Alectardy98/aek/aek.kicad_sch

## KiCad design aek.kicad_sch (2023-07-03)

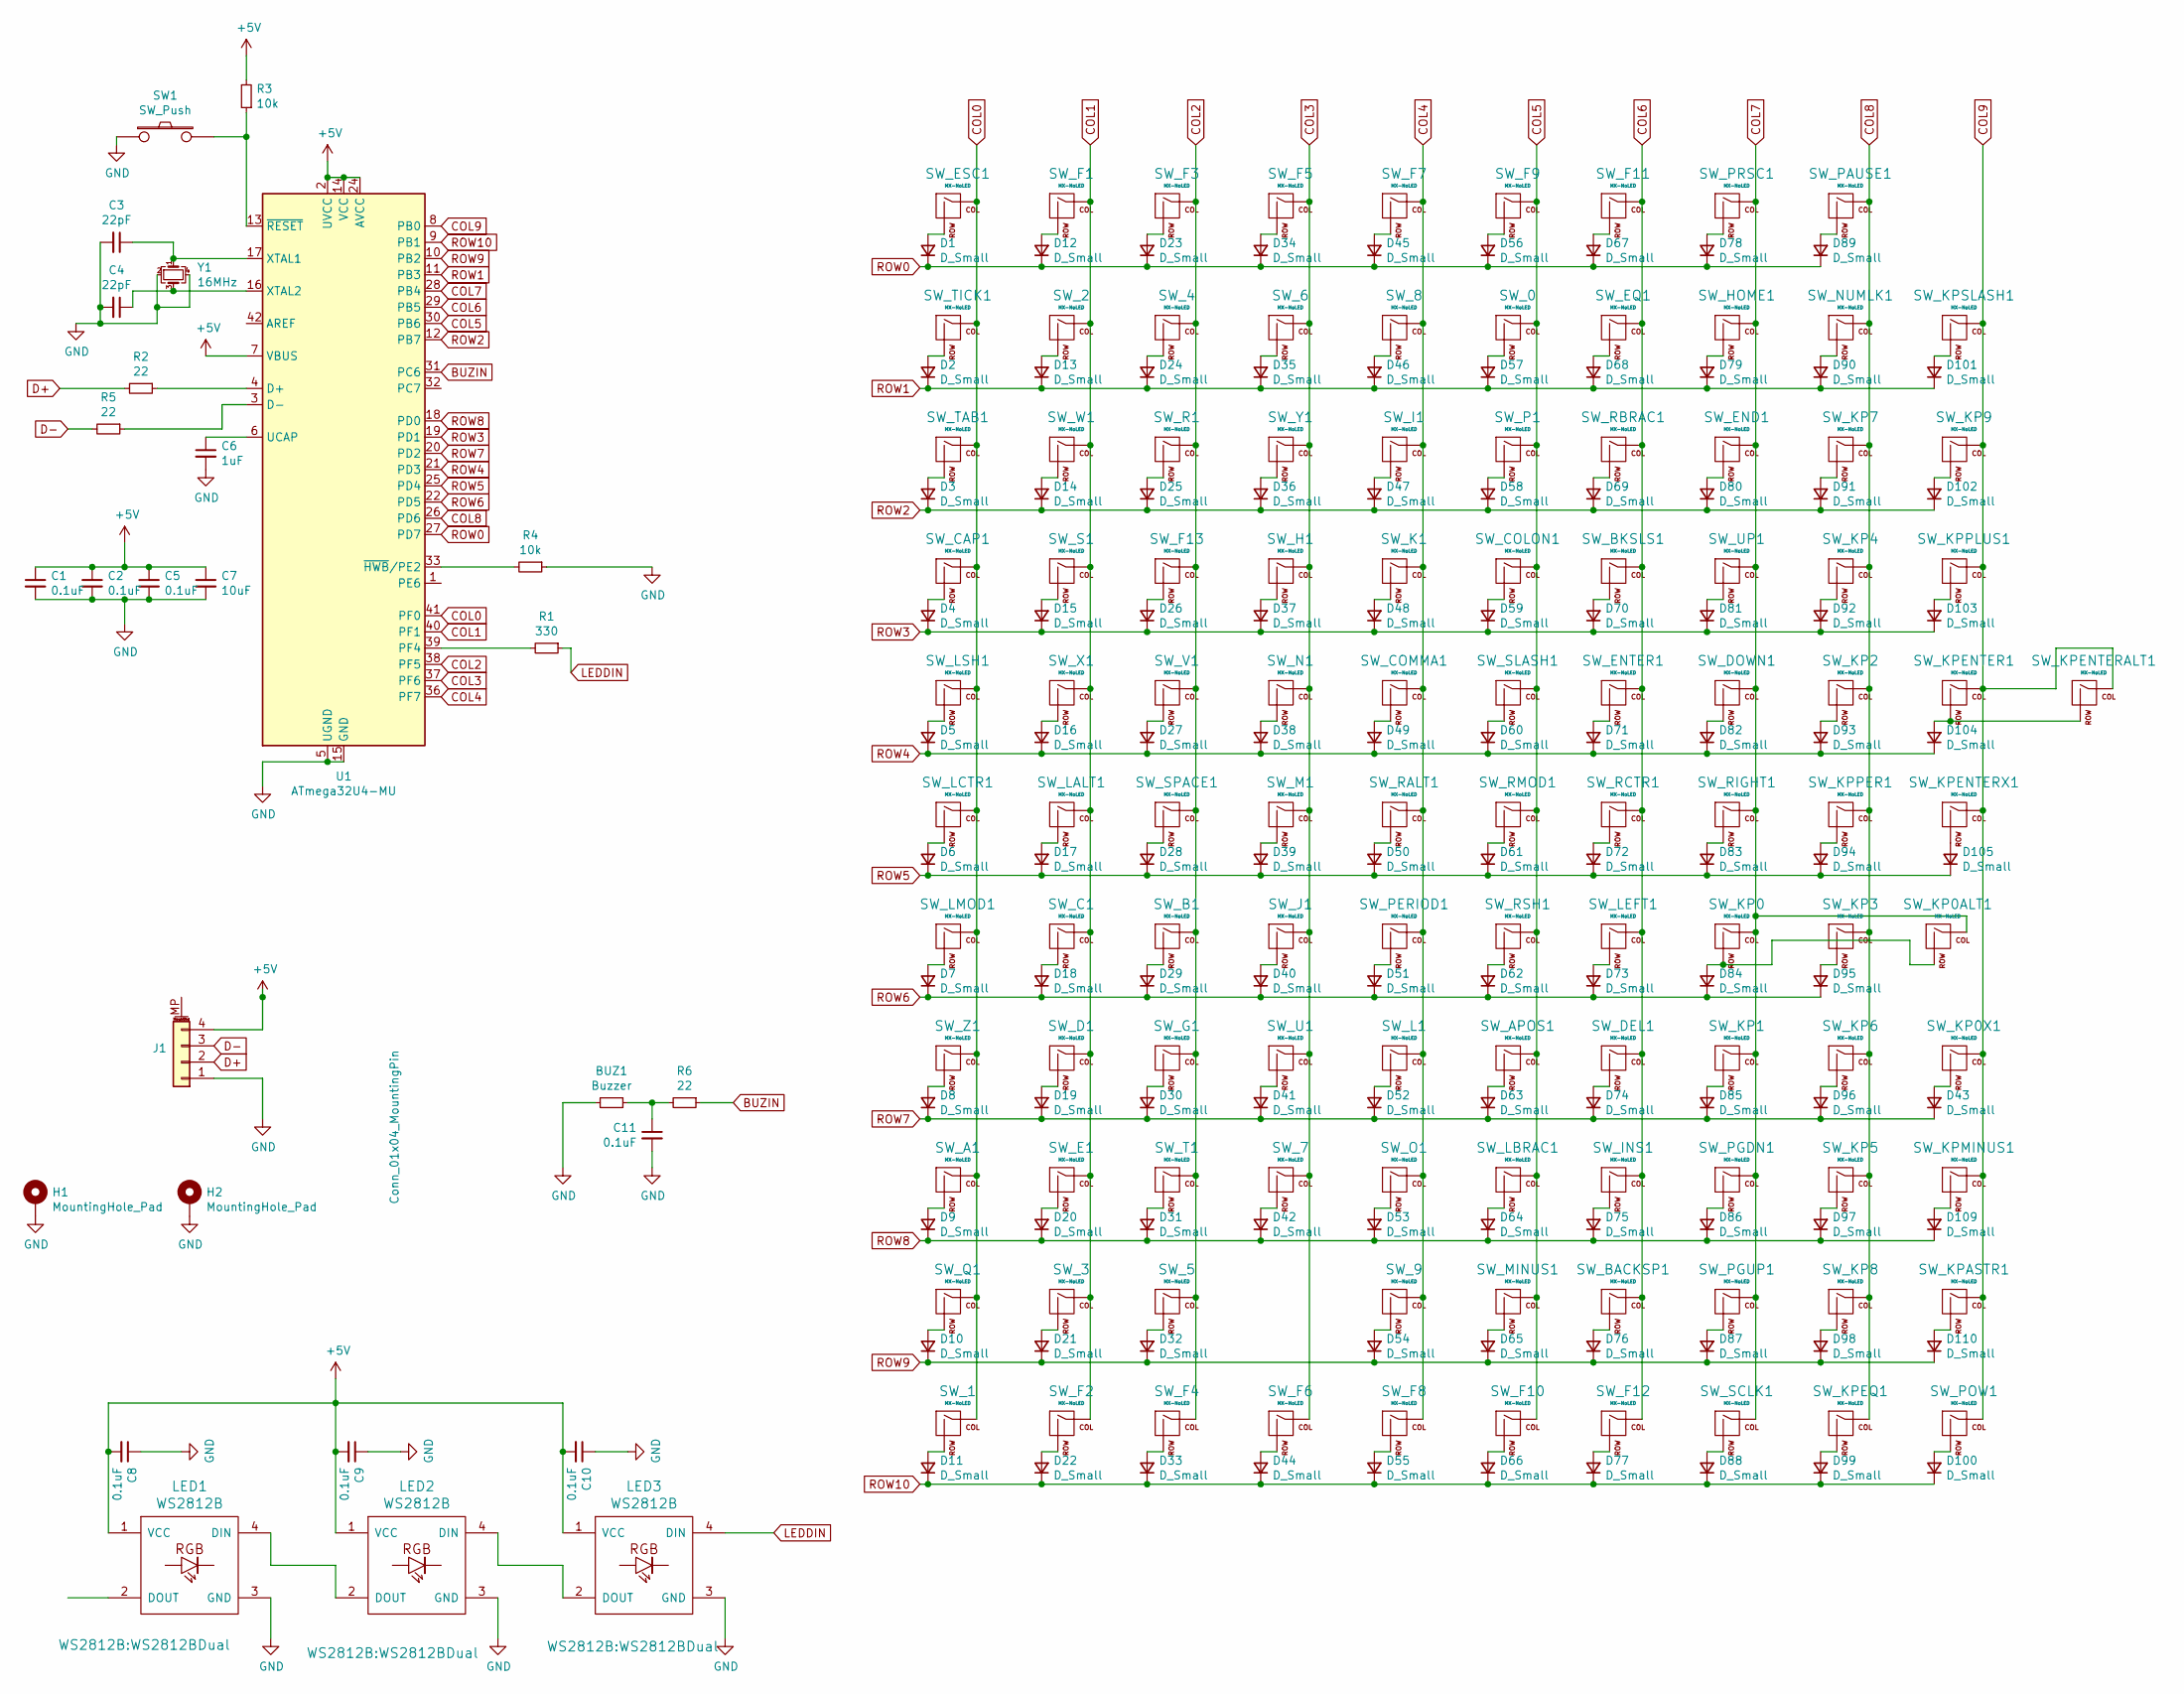
[picture p7: schematic aek.kicad_sch]

Parts:
BUZ1: Buzzer; Buzzer_Mallory_AST1109MLTRQ
C1, C2, C5, C8, C9, C10, C11: 0.1uF; C_0805_2012Metric
C3, C4: 22pF; C_0805_2012Metric
C6: 1uF; C_0805_2012Metric
C7: 10uF; C_0805_2012Metric
D1, D2, D3, D4, D5, D6, D7, D8, D9, D10, D11, D12, D13, D14, D15, D16, D17, D18, D19, D20, D21, D22, D23, D24, D25, D26, D27, D28, D29, D30, D31, D32, D33, D34, D35, D36, D37, D38, D39, D40, D41, D42, D43, D44, D45, D46, D47, D48, D49, D50, D51, D52, D53, D54, D55, D56, D57, D58, D59, D60, D61, D62, D63, D64, D65, D66, D67, D68, D69, D70, D71, D72, D73, D74, D75, D76, D77, D78, D79, D80, D81, D82, D83, D84, D85, D86, D87, D88, D89, D90, D91, D92, D93, D94, D95, D96, D97, D98, D99, D100, D101, D102, D103, D104, D105, D109, D110: D_Small; D_SOD-123
H1, H2: MountingHole_Pad; MountingHole_2.7mm_M2.5_Pad
J1: Conn_01x04_MountingPin; JST_SH_SM04B-SRSS-TB_1x04-1MP_P1.00mm_Horizontal
LED1, LED2, LED3: WS2812B; WS2812BDual
R1: 330; R_0805_2012Metric
R2, R5, R6: 22; R_0805_2012Metric
R3, R4: 10k; R_0805_2012Metric
SW1: SW_Push; SKQG-1155865
SW_0, SW_1, SW_2, SW_3, SW_4, SW_5, SW_6, SW_7, SW_8, SW_9: MX-NoLED; MX-1U-NoLED
SW_A1: MX-NoLED; MX-1U-NoLED
SW_APOS1: MX-NoLED; MX-1U-NoLED
SW_B1: MX-NoLED; MX-1U-NoLED
SW_BACKSP1: MX-NoLED; MX-2U-NoLED
SW_BKSLS1: MX-NoLED; MX-1.5U-NoLED
SW_C1: MX-NoLED; MX-1U-NoLED
SW_CAP1: MX-NoLED; MX-1.75U-NoLED
SW_COLON1: MX-NoLED; MX-1U-NoLED
SW_COMMA1: MX-NoLED; MX-1U-NoLED
SW_D1: MX-NoLED; MX-1U-NoLED
SW_DEL1: MX-NoLED; MX-1U-NoLED
SW_DOWN1: MX-NoLED; MX-1U-NoLED
SW_E1: MX-NoLED; MX-1U-NoLED
SW_END1: MX-NoLED; MX-1U-NoLED
SW_ENTER1: MX-NoLED; MX-2.25U-NoLED
SW_EQ1: MX-NoLED; MX-1U-NoLED
SW_ESC1: MX-NoLED; MX-1U-NoLED
SW_F1, SW_F2, SW_F3, SW_F4, SW_F5, SW_F6, SW_F7, SW_F8, SW_F9, SW_F10, SW_F11, SW_F12, SW_F13: MX-NoLED; MX-1U-NoLED
SW_G1: MX-NoLED; MX-1U-NoLED
SW_H1: MX-NoLED; MX-1U-NoLED
SW_HOME1: MX-NoLED; MX-1U-NoLED
SW_I1: MX-NoLED; MX-1U-NoLED
SW_INS1: MX-NoLED; MX-1U-NoLED
SW_J1: MX-NoLED; MX-1U-NoLED
SW_K1: MX-NoLED; MX-1U-NoLED
SW_KP0: MX-NoLED; MX-2U-ReversedStabilizers-NoLED
SW_KP0ALT1, SW_KP0X1, SW_KP1, SW_KP2, SW_KP3, SW_KP4, SW_KP5, SW_KP6, SW_KP7, SW_KP8, SW_KP9: MX-NoLED; MX-1U-NoLED
SW_KPASTR1: MX-NoLED; MX-1U-NoLED
SW_KPENTER1: MX-NoLED; MX-2U-ReversedStabilizers-NoLED
SW_KPENTERALT1: MX-NoLED; MX-1U-NoLED
SW_KPENTERX1: MX-NoLED; MX-1U-NoLED
SW_KPEQ1: MX-NoLED; MX-1U-NoLED
SW_KPMINUS1: MX-NoLED; MX-1U-NoLED
SW_KPPER1: MX-NoLED; MX-1U-NoLED
SW_KPPLUS1: MX-NoLED; MX-1U-NoLED
SW_KPSLASH1: MX-NoLED; MX-1U-NoLED
SW_L1: MX-NoLED; MX-1U-NoLED
SW_LALT1: MX-NoLED; MX-1.5U-NoLED
SW_LBRAC1: MX-NoLED; MX-1U-NoLED
SW_LCTR1: MX-NoLED; MX-1.5U-NoLED
SW_LEFT1: MX-NoLED; MX-1U-NoLED
SW_LMOD1: MX-NoLED; MX-1.25U-NoLED
SW_LSH1: MX-NoLED; MX-2.25U-NoLED
SW_M1: MX-NoLED; MX-1U-NoLED
SW_MINUS1: MX-NoLED; MX-1U-NoLED
SW_N1: MX-NoLED; MX-1U-NoLED
SW_NUMLK1: MX-NoLED; MX-1U-NoLED
SW_O1: MX-NoLED; MX-1U-NoLED
SW_P1: MX-NoLED; MX-1U-NoLED
SW_PAUSE1: MX-NoLED; MX-1U-NoLED
SW_PERIOD1: MX-NoLED; MX-1U-NoLED
SW_PGDN1: MX-NoLED; MX-1U-NoLED
SW_PGUP1: MX-NoLED; MX-1U-NoLED
SW_POW1: MX-NoLED; MX-1U-NoLED
SW_PRSC1: MX-NoLED; MX-1U-NoLED
SW_Q1: MX-NoLED; MX-1U-NoLED
SW_R1: MX-NoLED; MX-1U-NoLED
SW_RALT1: MX-NoLED; MX-1.5U-NoLED
SW_RBRAC1: MX-NoLED; MX-1U-NoLED
SW_RCTR1: MX-NoLED; MX-1.5U-NoLED
SW_RIGHT1: MX-NoLED; MX-1U-NoLED
SW_RMOD1: MX-NoLED; MX-1.25U-NoLED
SW_RSH1: MX-NoLED; MX-2.75U-NoLED
SW_S1: MX-NoLED; MX-1U-NoLED
SW_SCLK1: MX-NoLED; MX-1U-NoLED
SW_SLASH1: MX-NoLED; MX-1U-NoLED
SW_SPACE1: MX-NoLED; MX-6.5U-ReversedStabilizers-NoLED
SW_T1: MX-NoLED; MX-1U-NoLED
SW_TAB1: MX-NoLED; MX-1.5U-NoLED
SW_TICK1: MX-NoLED; MX-1U-NoLED
SW_U1: MX-NoLED; MX-1U-NoLED
SW_UP1: MX-NoLED; MX-1U-NoLED
SW_V1: MX-NoLED; MX-1U-NoLED
SW_W1: MX-NoLED; MX-1U-NoLED
SW_X1: MX-NoLED; MX-1U-NoLED
SW_Y1: MX-NoLED; MX-1U-NoLED
SW_Z1: MX-NoLED; MX-1U-NoLED
U1: ATmega32U4-MU; atmega32u4-mu-and-au
Y1: 16MHz; Crystal_SMD_3225-4Pin_3.2x2.5mm

Connections:
+5V: C1.1, C2.1, C5.1, C7.1, C8.2, C9.2, C10.2, J1.4, LED1.1 (VCC), LED2.1 (VCC), LED3.1 (VCC), R3.2, U1.2 (UVCC), U1.7 (VBUS), U1.14 (VCC), U1.24 (AVCC), U1.34 (VCC), U1.44 (AVCC)
BUZIN: R6.1, U1.31 (PC6)
COL0: SW_1.1 (COL), SW_A1.1 (COL), SW_CAP1.1 (COL), SW_ESC1.1 (COL), SW_LCTR1.1 (COL), SW_LMOD1.1 (COL), SW_LSH1.1 (COL), SW_Q1.1 (COL), SW_TAB1.1 (COL), SW_TICK1.1 (COL), SW_Z1.1 (COL), U1.41 (PF0)
COL1: SW_2.1 (COL), SW_3.1 (COL), SW_C1.1 (COL), SW_D1.1 (COL), SW_E1.1 (COL), SW_F1.1 (COL), SW_F2.1 (COL), SW_LALT1.1 (COL), SW_S1.1 (COL), SW_W1.1 (COL), SW_X1.1 (COL), U1.40 (PF1)
COL2: SW_4.1 (COL), SW_5.1 (COL), SW_B1.1 (COL), SW_F3.1 (COL), SW_F4.1 (COL), SW_F13.1 (COL), SW_G1.1 (COL), SW_R1.1 (COL), SW_SPACE1.1 (COL), SW_T1.1 (COL), SW_V1.1 (COL), U1.38 (PF5)
COL3: SW_6.1 (COL), SW_7.1 (COL), SW_F5.1 (COL), SW_F6.1 (COL), SW_H1.1 (COL), SW_J1.1 (COL), SW_M1.1 (COL), SW_N1.1 (COL), SW_U1.1 (COL), SW_Y1.1 (COL), U1.37 (PF6)
COL4: SW_8.1 (COL), SW_9.1 (COL), SW_COMMA1.1 (COL), SW_F7.1 (COL), SW_F8.1 (COL), SW_I1.1 (COL), SW_K1.1 (COL), SW_L1.1 (COL), SW_O1.1 (COL), SW_PERIOD1.1 (COL), SW_RALT1.1 (COL), U1.36 (PF7)
COL5: SW_0.1 (COL), SW_APOS1.1 (COL), SW_COLON1.1 (COL), SW_F9.1 (COL), SW_F10.1 (COL), SW_LBRAC1.1 (COL), SW_MINUS1.1 (COL), SW_P1.1 (COL), SW_RMOD1.1 (COL), SW_RSH1.1 (COL), SW_SLASH1.1 (COL), U1.30 (PB6)
COL6: SW_BACKSP1.1 (COL), SW_BKSLS1.1 (COL), SW_DEL1.1 (COL), SW_ENTER1.1 (COL), SW_EQ1.1 (COL), SW_F11.1 (COL), SW_F12.1 (COL), SW_INS1.1 (COL), SW_LEFT1.1 (COL), SW_RBRAC1.1 (COL), SW_RCTR1.1 (COL), U1.29 (PB5)
COL7: SW_DOWN1.1 (COL), SW_END1.1 (COL), SW_HOME1.1 (COL), SW_KP0.1 (COL), SW_KP0ALT1.1 (COL), SW_KP1.1 (COL), SW_PGDN1.1 (COL), SW_PGUP1.1 (COL), SW_PRSC1.1 (COL), SW_RIGHT1.1 (COL), SW_SCLK1.1 (COL), SW_UP1.1 (COL), U1.28 (PB4)
COL8: SW_KP2.1 (COL), SW_KP3.1 (COL), SW_KP4.1 (COL), SW_KP5.1 (COL), SW_KP6.1 (COL), SW_KP7.1 (COL), SW_KP8.1 (COL), SW_KPEQ1.1 (COL), SW_KPPER1.1 (COL), SW_NUMLK1.1 (COL), SW_PAUSE1.1 (COL), U1.26 (PD6)
COL9: SW_KP0X1.1 (COL), SW_KP9.1 (COL), SW_KPASTR1.1 (COL), SW_KPENTER1.1 (COL), SW_KPENTERALT1.1 (COL), SW_KPENTERX1.1 (COL), SW_KPMINUS1.1 (COL), SW_KPPLUS1.1 (COL), SW_KPSLASH1.1 (COL), SW_POW1.1 (COL), U1.8 (PB0)
D+: J1.2, R2.2
D-: J1.3, R5.2
GND: BUZ1.2, C1.2, C2.2, C3.2, C4.2, C5.2, C6.2, C7.2, C8.1, C9.1, C10.1, C11.2, H1.1, H2.1, J1.1, LED1.3 (GND), LED2.3 (GND), LED3.3 (GND), R4.1, SW1.1, U1.5 (UGND), U1.15 (GND), U1.23 (GND), U1.35 (GND), U1.43 (GND), U1.45 (GND), Y1.2, Y1.4
LEDDIN: LED3.4 (DIN), R1.1
unnamed: BUZ1.1, C11.1, R6.2
unnamed: C3.1, U1.17 (XTAL1), Y1.1
unnamed: C4.1, U1.16 (XTAL2), Y1.3
unnamed: C6.1, U1.6 (UCAP)
unnamed: D1.2 (A), SW_ESC1.2 (ROW)
unnamed: D2.2 (A), SW_TICK1.2 (ROW)
unnamed: D3.2 (A), SW_TAB1.2 (ROW)
unnamed: D4.2 (A), SW_CAP1.2 (ROW)
unnamed: D5.2 (A), SW_LSH1.2 (ROW)
unnamed: D6.2 (A), SW_LCTR1.2 (ROW)
unnamed: D7.2 (A), SW_LMOD1.2 (ROW)
unnamed: D8.2 (A), SW_Z1.2 (ROW)
unnamed: D9.2 (A), SW_A1.2 (ROW)
unnamed: D10.2 (A), SW_Q1.2 (ROW)
unnamed: D11.2 (A), SW_1.2 (ROW)
unnamed: D12.2 (A), SW_F1.2 (ROW)
unnamed: D13.2 (A), SW_2.2 (ROW)
unnamed: D14.2 (A), SW_W1.2 (ROW)
unnamed: D15.2 (A), SW_S1.2 (ROW)
unnamed: D16.2 (A), SW_X1.2 (ROW)
unnamed: D17.2 (A), SW_LALT1.2 (ROW)
unnamed: D18.2 (A), SW_C1.2 (ROW)
unnamed: D19.2 (A), SW_D1.2 (ROW)
unnamed: D20.2 (A), SW_E1.2 (ROW)
unnamed: D21.2 (A), SW_3.2 (ROW)
unnamed: D22.2 (A), SW_F2.2 (ROW)
unnamed: D23.2 (A), SW_F3.2 (ROW)
unnamed: D24.2 (A), SW_4.2 (ROW)
unnamed: D25.2 (A), SW_R1.2 (ROW)
unnamed: D26.2 (A), SW_F13.2 (ROW)
unnamed: D27.2 (A), SW_V1.2 (ROW)
unnamed: D28.2 (A), SW_SPACE1.2 (ROW)
unnamed: D29.2 (A), SW_B1.2 (ROW)
unnamed: D30.2 (A), SW_G1.2 (ROW)
unnamed: D31.2 (A), SW_T1.2 (ROW)
unnamed: D32.2 (A), SW_5.2 (ROW)
unnamed: D33.2 (A), SW_F4.2 (ROW)
unnamed: D34.2 (A), SW_F5.2 (ROW)
unnamed: D35.2 (A), SW_6.2 (ROW)
unnamed: D36.2 (A), SW_Y1.2 (ROW)
unnamed: D37.2 (A), SW_H1.2 (ROW)
unnamed: D38.2 (A), SW_N1.2 (ROW)
unnamed: D39.2 (A), SW_M1.2 (ROW)
unnamed: D40.2 (A), SW_J1.2 (ROW)
unnamed: D41.2 (A), SW_U1.2 (ROW)
unnamed: D42.2 (A), SW_7.2 (ROW)
unnamed: D43.2 (A), SW_KP0X1.2 (ROW)
unnamed: D44.2 (A), SW_F6.2 (ROW)
unnamed: D45.2 (A), SW_F7.2 (ROW)
unnamed: D46.2 (A), SW_8.2 (ROW)
unnamed: D47.2 (A), SW_I1.2 (ROW)
unnamed: D48.2 (A), SW_K1.2 (ROW)
unnamed: D49.2 (A), SW_COMMA1.2 (ROW)
unnamed: D50.2 (A), SW_RALT1.2 (ROW)
unnamed: D51.2 (A), SW_PERIOD1.2 (ROW)
unnamed: D52.2 (A), SW_L1.2 (ROW)
unnamed: D53.2 (A), SW_O1.2 (ROW)
unnamed: D54.2 (A), SW_9.2 (ROW)
unnamed: D55.2 (A), SW_F8.2 (ROW)
unnamed: D56.2 (A), SW_F9.2 (ROW)
unnamed: D57.2 (A), SW_0.2 (ROW)
unnamed: D58.2 (A), SW_P1.2 (ROW)
unnamed: D59.2 (A), SW_COLON1.2 (ROW)
unnamed: D60.2 (A), SW_SLASH1.2 (ROW)
unnamed: D61.2 (A), SW_RMOD1.2 (ROW)
unnamed: D62.2 (A), SW_RSH1.2 (ROW)
unnamed: D63.2 (A), SW_APOS1.2 (ROW)
unnamed: D64.2 (A), SW_LBRAC1.2 (ROW)
unnamed: D65.2 (A), SW_MINUS1.2 (ROW)
unnamed: D66.2 (A), SW_F10.2 (ROW)
unnamed: D67.2 (A), SW_F11.2 (ROW)
unnamed: D68.2 (A), SW_EQ1.2 (ROW)
unnamed: D69.2 (A), SW_RBRAC1.2 (ROW)
unnamed: D70.2 (A), SW_BKSLS1.2 (ROW)
unnamed: D71.2 (A), SW_ENTER1.2 (ROW)
unnamed: D72.2 (A), SW_RCTR1.2 (ROW)
unnamed: D73.2 (A), SW_LEFT1.2 (ROW)
unnamed: D74.2 (A), SW_DEL1.2 (ROW)
unnamed: D75.2 (A), SW_INS1.2 (ROW)
unnamed: D76.2 (A), SW_BACKSP1.2 (ROW)
unnamed: D77.2 (A), SW_F12.2 (ROW)
unnamed: D78.2 (A), SW_PRSC1.2 (ROW)
unnamed: D79.2 (A), SW_HOME1.2 (ROW)
unnamed: D80.2 (A), SW_END1.2 (ROW)
unnamed: D81.2 (A), SW_UP1.2 (ROW)
unnamed: D82.2 (A), SW_DOWN1.2 (ROW)
unnamed: D83.2 (A), SW_RIGHT1.2 (ROW)
unnamed: D84.2 (A), SW_KP0.2 (ROW), SW_KP0ALT1.2 (ROW)
unnamed: D85.2 (A), SW_KP1.2 (ROW)
unnamed: D86.2 (A), SW_PGDN1.2 (ROW)
unnamed: D87.2 (A), SW_PGUP1.2 (ROW)
unnamed: D88.2 (A), SW_SCLK1.2 (ROW)
unnamed: D89.2 (A), SW_PAUSE1.2 (ROW)
unnamed: D90.2 (A), SW_NUMLK1.2 (ROW)
unnamed: D91.2 (A), SW_KP7.2 (ROW)
unnamed: D92.2 (A), SW_KP4.2 (ROW)
unnamed: D93.2 (A), SW_KP2.2 (ROW)
unnamed: D94.2 (A), SW_KPPER1.2 (ROW)
unnamed: D95.2 (A), SW_KP3.2 (ROW)
unnamed: D96.2 (A), SW_KP6.2 (ROW)
unnamed: D97.2 (A), SW_KP5.2 (ROW)
unnamed: D98.2 (A), SW_KP8.2 (ROW)
unnamed: D99.2 (A), SW_KPEQ1.2 (ROW)
unnamed: D100.2 (A), SW_POW1.2 (ROW)
unnamed: D101.2 (A), SW_KPSLASH1.2 (ROW)
unnamed: D102.2 (A), SW_KP9.2 (ROW)
unnamed: D103.2 (A), SW_KPPLUS1.2 (ROW)
unnamed: D104.2 (A), SW_KPENTER1.2 (ROW), SW_KPENTERALT1.2 (ROW)
unnamed: D105.2 (A), SW_KPENTERX1.2 (ROW)
unnamed: D109.2 (A), SW_KPMINUS1.2 (ROW)
unnamed: D110.2 (A), SW_KPASTR1.2 (ROW)
unnamed: LED1.4 (DIN), LED2.2 (DOUT)
unnamed: LED2.4 (DIN), LED3.2 (DOUT)
unnamed: R1.2, U1.39 (PF4)
unnamed: R2.1, U1.4 (D+)
unnamed: R3.1, SW1.2, U1.13 (~RESET)
unnamed: R4.2, U1.33 (~HWB/PE2)
unnamed: R5.1, U1.3 (D-)
ROW0: D1.1 (K), D12.1 (K), D23.1 (K), D34.1 (K), D45.1 (K), D56.1 (K), D67.1 (K), D78.1 (K), D89.1 (K), U1.27 (PD7)
ROW1: D2.1 (K), D13.1 (K), D24.1 (K), D35.1 (K), D46.1 (K), D57.1 (K), D68.1 (K), D79.1 (K), D90.1 (K), D101.1 (K), U1.11 (PB3)
ROW2: D3.1 (K), D14.1 (K), D25.1 (K), D36.1 (K), D47.1 (K), D58.1 (K), D69.1 (K), D80.1 (K), D91.1 (K), D102.1 (K), U1.12 (PB7)
ROW3: D4.1 (K), D15.1 (K), D26.1 (K), D37.1 (K), D48.1 (K), D59.1 (K), D70.1 (K), D81.1 (K), D92.1 (K), D103.1 (K), U1.19 (PD1)
ROW4: D5.1 (K), D16.1 (K), D27.1 (K), D38.1 (K), D49.1 (K), D60.1 (K), D71.1 (K), D82.1 (K), D93.1 (K), D104.1 (K), U1.21 (PD3)
ROW5: D6.1 (K), D17.1 (K), D28.1 (K), D39.1 (K), D50.1 (K), D61.1 (K), D72.1 (K), D83.1 (K), D94.1 (K), D105.1 (K), U1.25 (PD4)
ROW6: D7.1 (K), D18.1 (K), D29.1 (K), D40.1 (K), D51.1 (K), D62.1 (K), D73.1 (K), D84.1 (K), D95.1 (K), U1.22 (PD5)
ROW7: D8.1 (K), D19.1 (K), D30.1 (K), D41.1 (K), D43.1 (K), D52.1 (K), D63.1 (K), D74.1 (K), D85.1 (K), D96.1 (K), U1.20 (PD2)
ROW8: D9.1 (K), D20.1 (K), D31.1 (K), D42.1 (K), D53.1 (K), D64.1 (K), D75.1 (K), D86.1 (K), D97.1 (K), D109.1 (K), U1.18 (PD0)
ROW9: D10.1 (K), D21.1 (K), D32.1 (K), D54.1 (K), D65.1 (K), D76.1 (K), D87.1 (K), D98.1 (K), D110.1 (K), U1.10 (PB2)
ROW10: D11.1 (K), D22.1 (K), D33.1 (K), D44.1 (K), D55.1 (K), D66.1 (K), D77.1 (K), D88.1 (K), D99.1 (K), D100.1 (K), U1.9 (PB1)
